ivomirb/Controlinator-3000/Source/Emulator/resource.h

//{{NO_DEPENDENCIES}}
// Microsoft Visual C++ generated include file.
// Used by Emulator.rc
//
#define IDC_MYICON                      2
#define IDD_PENDANTEMULATOR_DIALOG      102
#define IDS_APP_TITLE                   103
#define IDD_ABOUTBOX                    103
#define IDM_ABOUT                       104
#define IDM_EXIT                        105
#define IDI_PENDANTEMULATOR             107
#define IDI_SMALL                       108
#define IDC_PENDANTEMULATOR             109
#define IDR_MAINFRAME                   128
#define IDD_CONSOLE                     129
#define IDC_EDITOUTPUT                  1001
#define IDC_BUTTON1                     1002
#define IDC_BUTTONCLEAR                 1002
#define ID_FILE_GAMEPAD                 32771
#define IDC_STATIC                      -1

// Next default values for new objects
// 
#ifdef APSTUDIO_INVOKED
#ifndef APSTUDIO_READONLY_SYMBOLS
#define _APS_NO_MFC                     1
#define _APS_NEXT_RESOURCE_VALUE        130
#define _APS_NEXT_COMMAND_VALUE         32772
#define _APS_NEXT_CONTROL_VALUE         1003
#define _APS_NEXT_SYMED_VALUE           110
#endif
#endif
